ugougo1972/digital-kakejiku/90_DECISIONS/030_SYSTEM/DECISION_203_DEVELOPMENT_STATEGY.md

# Discussion: 開発戦略と先行調達方針

## 概要

本プロジェクトでは、
部材選定そのものよりも、

```text
「開発停止を防ぐこと」
```

を重視する。

そのため、
必要部材を粗く洗い出した段階で、
AliExpress 等を用いて先行発注を行う。

---

# 背景

ESP32系開発では、
以下がボトルネック化しやすい。

- 海外部材納期
- 在庫切れ
- 互換部材調査
- E-Paper入荷待ち
- センサ納期
- UI部材探索

特に：

- E-Paper
- CO2センサ
- UIノブ
- 特殊センサ

は納期が長くなりやすい。

---

# 現在の基本戦略

```text
必要部材を粗く洗い出す
↓
AliExpress等で先行発注
↓
輸送待ち期間中に
ESP32 / GAS / GitHub整備
```

を基本戦略とする。

---

# この戦略を採用する理由

## 1. 開発停止回避

最も大きい理由。

「次工程へ進めない」
状態を避ける。

---

## 2. ソフト開発を止めない

現在の主工程は：

- ESP32 HTTPS POST
- GAS
- Spreadsheet
- GitHub整備

であり、
センサ現物が無くても進行可能。

---

## 3. ESP32系は後付統合が比較的容易

I2C中心構成を採用しているため：

- BME280
- LTR390
- SCD40
- ENS160

などは後段統合しやすい。

---

# GitHub文書について

本プロジェクトでは、
GitHub文書整備を
独立した重要タスクとして扱う。

理由：

- 設計散逸防止
- 次チャット引継ぎ容易化
- 長期開発耐性
- 将来自己参照性

---

# 現時点の優先順位

## 最優先

- 電源安定化
- ESP32 HTTPS POST
- Serial Monitor可視化

## 高

- GitHubドキュメント同期
- Spreadsheet構造整理

## 中

- センサ統合
- UI統合

## 後段

- Gemini高度化
- 筐体化
- OTA
