ugougo1972/digital-kakejiku/91_DISCUSSION/040_UI/DISCUSSION_UI_JOGDIAL.md

# Discussion: ジョグダイヤル主体UI構想

## 概要

本プロジェクトでは、
ジョグダイヤル主体UIを有力候補として検討中。

---

# 想定UI

## 入力装置

- RGB LED付きロータリーエンコーダ
- 大径ノブ
- 押下スイッチ

---

# 採用理由

## 1. 据置型との相性

片手操作しやすい。

---

## 2. 操作数削減

複数ボタンを減らせる。

---

## 3. 静的UIとの整合性

本プロジェクトでは：

- 常時アニメーション
- 高頻度操作
- 派手な演出

よりも：

- 静けさ
- 緩慢
- 余白

を重視する。

ジョグダイヤルはこの思想と整合する。

---

# 想定操作

| 操作 | 動作 |
|---|---|
| 右回転 | 次項目 |
| 左回転 | 前項目 |
| 短押し | 決定 |
| 長押し | メニュー |
| 押しながら回転 | 高速送り |

---

# 表示思想

## 現在有力

- E-Paper

## 理由

- 非発光
- 静的表示
- 低頻度更新
- 電子的掛軸との整合性

---

# 現段階の方針

UI高度化は後段。

現在最優先は：

```text
ESP32 ↔ GAS HTTPS POST
```

である。

UIは通信基盤安定化後に統合する。
