ugougo1972/digital-kakejiku/90_DECISIONS/DISCUSSION_005_PROJECT_STATUS.md

# Discussion 005
# 開発状況

完了:

- GAS通信PoC
- HTTPS POST
- DeepSleep周期送信
- Spreadsheet保存

進行中:

- UPS評価
- センサ統合
- 音環境PoC

未着手:

- E-Paper描画
- UI統合
- 長期運用試験
