ugougo1972/digital-kakejiku/90_DECISIONS/030_SYSTEM/DECISION_201_PROJECT_DIRECTION.md

# DECISION_0001_PROJECT_DIRECTION.md

# Decision

プロジェクトを
「静的観測装置」
として定義する。

---

# Date

2026-05-27

---

# Status

Accepted

---

# Context

本プロジェクトは当初、
ESP32系環境Dataロガーの延長として開始された。

しかし検討の結果、
単なる環境表示装置ではなく、

- 空気感
- 季節感
- 滞在感
- 時間性
- AI生成文

を含む、
「個人的観測装置」
として方向性を定義した。

---

# Decision Details

本プロジェクトでは：

- 高FPS
- 派手なUI
- 常時アニメーション
- ダッシュボード化

を優先しない。

代わりに：

- 静止
- 余白
- 緩慢な変化
- 時系列性
- 空気感

を重視する。

---

# Consequences

## Positive

- プロジェクト思想が明確になる
- UI暴走を抑制できる
- E-Paperとの整合性が高い
- 長期観測思想と一致する

## Negative

- 一般的IoT機器とは方向性が異なる
- 派手なデモ性は低下する
